nerpatech/tek-ct-adapters/img/to252-banana-plug-inserted-back.png

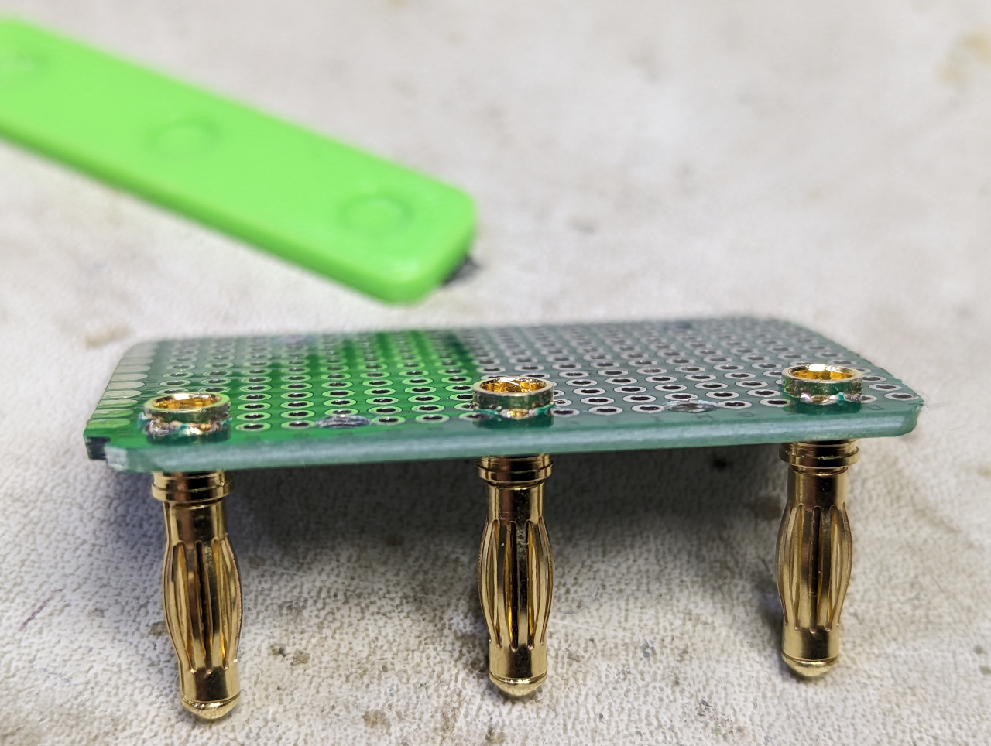
img/to252-banana-plug-inserted-back.png
