nerpatech/tek-ct-adapters/img/to252-pcb-banana-plug-holes-drilled.png

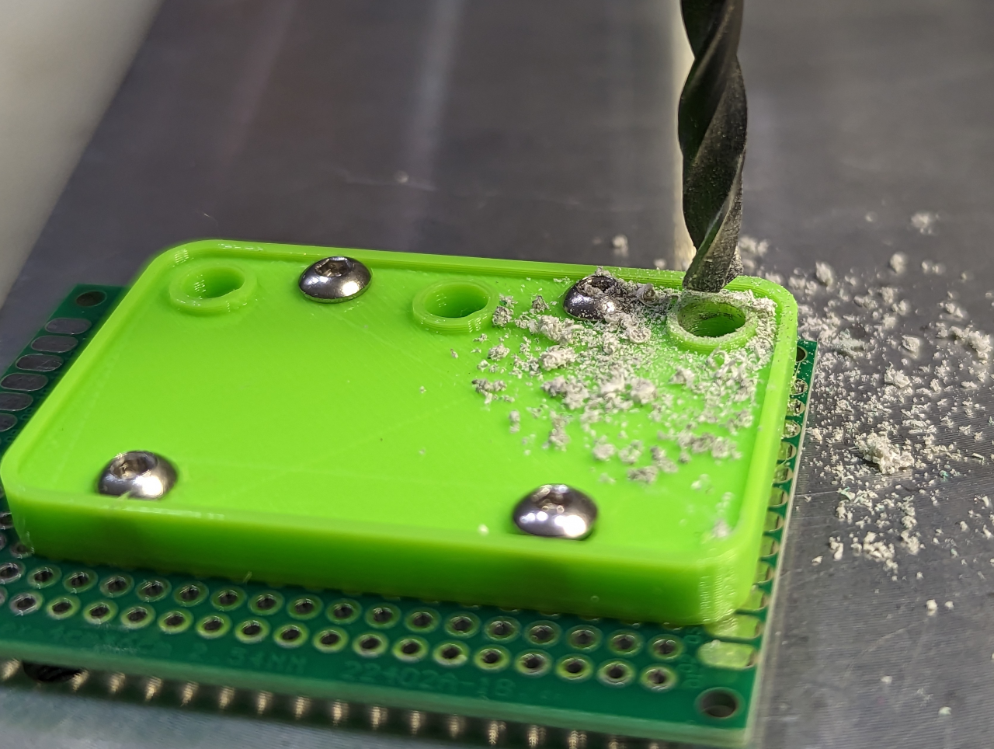
img/to252-pcb-banana-plug-holes-drilled.png
