nerpatech/tek-ct-adapters/img/to252-pcb-screw-holes-drilled.png

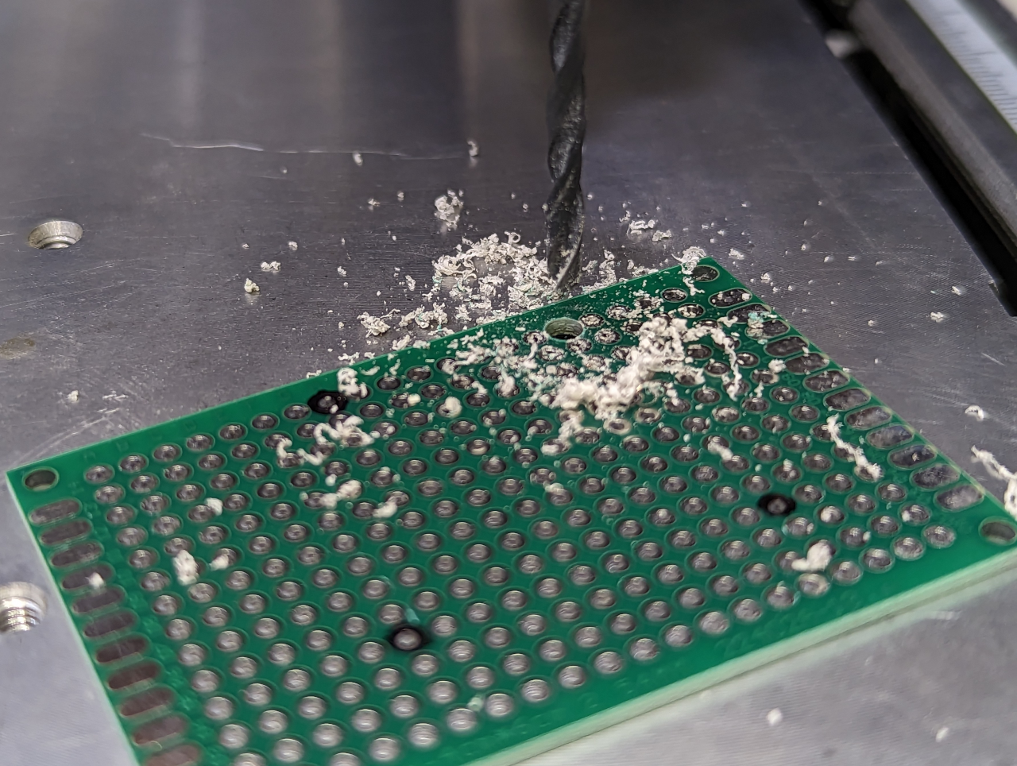
img/to252-pcb-screw-holes-drilled.png
