nerpatech/tek-ct-adapters/img/to252-adapter-assembled-back.png

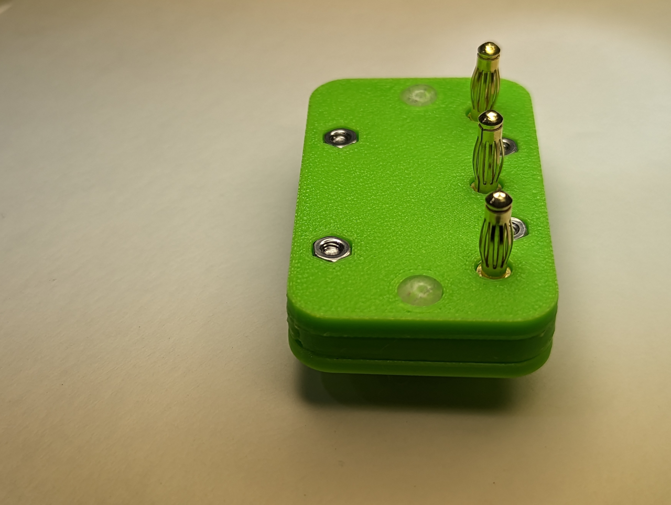
img/to252-adapter-assembled-back.png
