nerpatech/tek-ct-adapters/img/to252-adapter-assembled-front.png

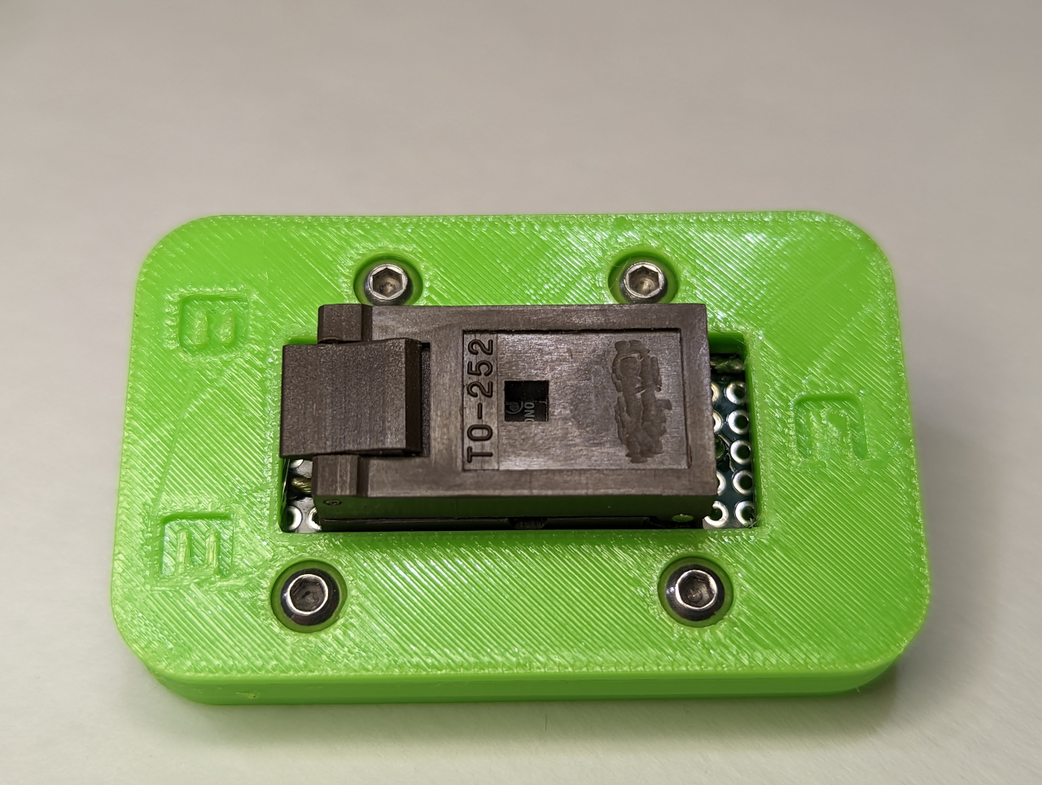
img/to252-adapter-assembled-front.png
