nerpatech/tek-ct-adapters/img/to252-plugs-soldered.png

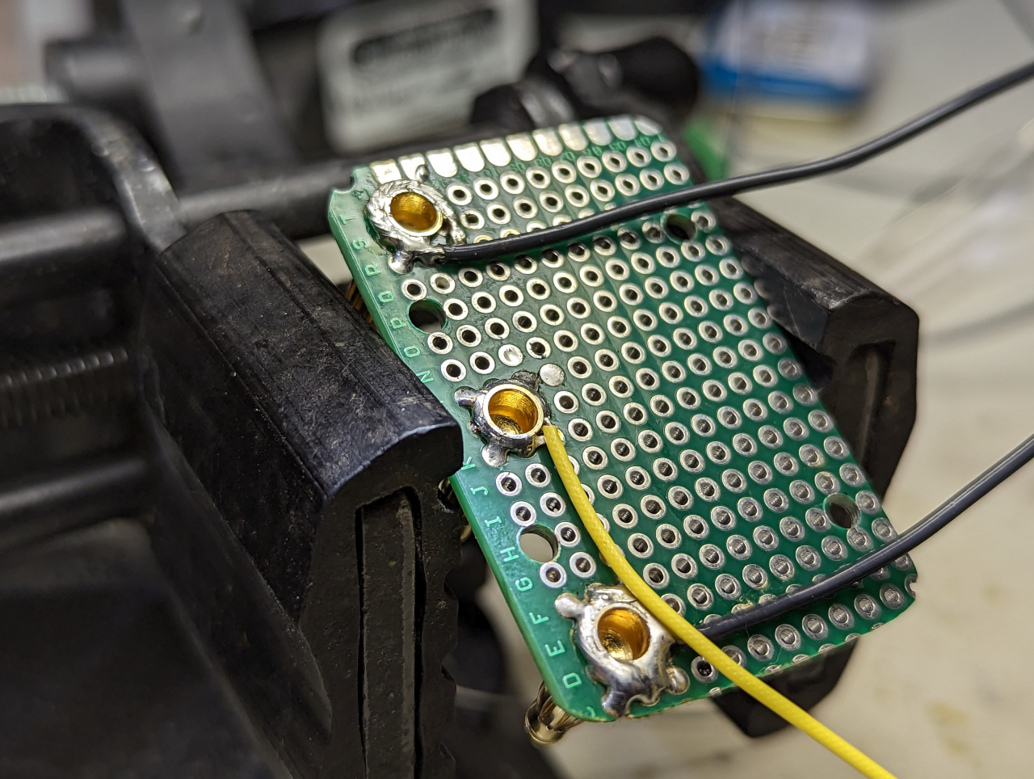
img/to252-plugs-soldered.png
